jumangee/EcoSenseAtclock/EcosenseAtClock/mq4sensor_process.h

/**
 * MQ-4 process
 * for Processy Firmware Framework
 */
 
#ifndef _MQ4_SENSOR_PROCESS_H
#define _MQ4_SENSOR_PROCESS_H

#include "processy.h"
#include "processy_process.h"

#include "ecosense_cfg.h"
#include "mqsensor_process.h"

class MQ4SensorProcess: public MQSensorProcess {
	public:
		PROCESSID(PRC_MQ4);
		
		MQ4SensorProcess(IProcessMessage* msg);

		static IFirmwareProcess* factory(IProcessMessage* msg);

		IProcessMessage* getResultMsg();

};

#endif
