jumangee/EcoSenseAtclock/EcosenseAtClock/EspDrv/EspDrv.h

/*--------------------------------------------------------------------
This file is part of the Arduino WiFiEsp library.

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
You should have received a copy of the GNU General Public License
along with The Arduino WiFiEsp library.  If not, see
<http://www.gnu.org/licenses/>.
--------------------------------------------------------------------*/

#ifndef EspDrv_h
#define EspDrv_h

#include "Stream.h"
#include "IPAddress.h"


#include "RingBuffer.h"



// Maximum size of a SSID
#define WL_SSID_MAX_LENGTH 32

// Size of a MAC-address or BSSID
#define WL_MAC_ADDR_LENGTH 6

// Size of a MAC-address or BSSID
#define WL_IPV4_LENGTH 4

// Maximum size of a SSID list
#define WL_NETWORKS_LIST_MAXNUM	10

// Maxmium number of socket
#define	MAX_SOCK_NUM		4

// Socket not available constant
#define SOCK_NOT_AVAIL  255

// Default state value for Wifi state field
#define NA_STATE -1

#define WL_FW_VER_LENGTH 6

#define NO_SOCKET_AVAIL 255


// maximum size of AT command
#define CMD_BUFFER_SIZE 200


typedef enum eProtMode {TCP_MODE, UDP_MODE, SSL_MODE} tProtMode;


typedef enum {
        WL_FAILURE = -1,
        WL_SUCCESS = 1,
} wl_error_code_t;

/* Authentication modes */
enum wl_auth_mode {
        AUTH_MODE_INVALID,
        AUTH_MODE_AUTO,
        AUTH_MODE_OPEN_SYSTEM,
        AUTH_MODE_SHARED_KEY,
        AUTH_MODE_WPA,
        AUTH_MODE_WPA2,
        AUTH_MODE_WPA_PSK,
        AUTH_MODE_WPA2_PSK
};


typedef enum {
	WL_NO_SHIELD = 255,
	WL_IDLE_STATUS = 0,
	//WL_NO_SSID_AVAIL,
	//WL_SCAN_COMPLETED,
	WL_CONNECTED,
	WL_CONNECT_FAILED,
	//WL_CONNECTION_LOST,
	WL_DISCONNECTED
} wl_status_t;

/* Encryption modes */
enum wl_enc_type {
	ENC_TYPE_NONE = 0,
	ENC_TYPE_WEP = 1,
	ENC_TYPE_WPA_PSK = 2,
	ENC_TYPE_WPA2_PSK = 3,
	ENC_TYPE_WPA_WPA2_PSK = 4
};


enum wl_tcp_state {
	CLOSED      = 0,
	LISTEN      = 1,
	SYN_SENT    = 2,
	SYN_RCVD    = 3,
	ESTABLISHED = 4,
	FIN_WAIT_1  = 5,
	FIN_WAIT_2  = 6,
	CLOSE_WAIT  = 7,
	CLOSING     = 8,
	LAST_ACK    = 9,
	TIME_WAIT   = 10
};



class EspDrv
{

public:

    static void wifiDriverInit(Stream *espSerial);


    /* Start Wifi connection with passphrase
     *
     * param ssid: Pointer to the SSID string.
     * param passphrase: Passphrase. Valid characters in a passphrase must be between ASCII 32-126 (decimal).
     */
    static bool wifiConnect(const char* ssid, const char* passphrase);


    /*
	* Start the Access Point
	*/
	static bool wifiStartAP(const char* ssid, const char* pwd, uint8_t channel, uint8_t enc, uint8_t espMode);


    /*
	 * Set ip configuration disabling dhcp client
	 */
    //static void config(IPAddress local_ip);

    /*
	 * Set ip configuration disabling dhcp client
	 */
    //static void configAP(IPAddress local_ip);


    /*
     * Disconnect from the network
     *
     * return: WL_SUCCESS or WL_FAILURE
     */
    static int8_t disconnect();

    /*
     *
     *
     * return: one value of wl_status_t enum
     */
    static uint8_t getConnectionStatus();

    /*
     * Get the interface MAC address.
     *
     * return: pointer to uint8_t array with length WL_MAC_ADDR_LENGTH
     */
    //static uint8_t* getMacAddress();

    /*
     * Get the interface IP address.
     *
     * return: copy the ip address value in IPAddress object
     */
    /*static void getIpAddress(IPAddress& ip);

	static void getIpAddressAP(IPAddress& ip);*/

    /*
     * Get the interface IP netmask.
     * This can be used to retrieve settings configured through DHCP.
     *
     * return: true if successful
     */
    //static bool getNetmask(IPAddress& mask);

    /*
     * Get the interface IP gateway.
     * This can be used to retrieve settings configured through DHCP.
     *
     * return: true if successful
     */
    //static bool getGateway(IPAddress& mask);

    /*
     * Return the current SSID associated with the network
     *
     * return: ssid string
     */
    //static char* getCurrentSSID();

    /*
     * Return the current BSSID associated with the network.
     * It is the MAC address of the Access Point
     *
     * return: pointer to uint8_t array with length WL_MAC_ADDR_LENGTH
     */
    //static uint8_t* getCurrentBSSID();

    /*
     * Return the current RSSI /Received Signal Strength in dBm)
     * associated with the network
     *
     * return: signed value
     */
    static int32_t getCurrentRSSI();

    /*
     * Get the networks available
     *
     * return: Number of discovered networks
     */
    //static uint8_t getScanNetworks();

	/*
     * Return the SSID discovered during the network scan.
     *
     * param networkItem: specify from which network item want to get the information
	 *
     * return: ssid string of the specified item on the networks scanned list
     */
    //static char* getSSIDNetoworks(uint8_t networkItem);

    /*
     * Return the RSSI of the networks discovered during the scanNetworks
     *
     * param networkItem: specify from which network item want to get the information
	 *
     * return: signed value of RSSI of the specified item on the networks scanned list
     */
    //static int32_t getRSSINetoworks(uint8_t networkItem);

    /*
     * Return the encryption type of the networks discovered during the scanNetworks
     *
     * param networkItem: specify from which network item want to get the information
	 *
     * return: encryption type (enum wl_enc_type) of the specified item on the networks scanned list
     */
    //static uint8_t getEncTypeNetowrks(uint8_t networkItem);


    /*
     * Get the firmware version
     */
    static char* getFwVersion();


	////////////////////////////////////////////////////////////////////////////
	// Client/Server methods
	////////////////////////////////////////////////////////////////////////////


    //static bool startServer(uint16_t port, uint8_t sock);
    static bool startClient(const char* host, uint16_t port, uint8_t sock, uint8_t protMode);
    static void stopClient(uint8_t sock);
    //static uint8_t getServerState(uint8_t sock);
    static uint8_t getClientState(uint8_t sock);
    static bool getData(uint8_t connId, uint8_t *data, bool peek, bool* connClose);
    static int getDataBuf(uint8_t connId, uint8_t *buf, uint16_t bufSize);
    static bool sendData(uint8_t sock, const uint8_t *data, uint16_t len);
    static bool sendData(uint8_t sock, const __FlashStringHelper *data, uint16_t len, bool appendCrLf=false);
	static bool sendDataUdp(uint8_t sock, const char* host, uint16_t port, const uint8_t *data, uint16_t len);
    static uint16_t availData(uint8_t connId);


	static bool ping(const char *host);
    static void reset();

    //static void getRemoteIpAddress(IPAddress& ip);
    //static uint16_t getRemotePort();


////////////////////////////////////////////////////////////////////////////////

private:
	static Stream *espSerial;

	static long _bufPos;
	static uint8_t _connId;

	static uint16_t _remotePort;
	static uint8_t  _remoteIp[WL_IPV4_LENGTH];


	// firmware version string
	static char 	fwVersion[WL_FW_VER_LENGTH];

	// settings of requested network
	/*static char 	_networkSsid[WL_NETWORKS_LIST_MAXNUM][WL_SSID_MAX_LENGTH];
	static int32_t 	_networkRssi[WL_NETWORKS_LIST_MAXNUM];
	static uint8_t 	_networkEncr[WL_NETWORKS_LIST_MAXNUM];*/


	// settings of current selected network
	static char 	_ssid[WL_SSID_MAX_LENGTH];
	static uint8_t 	_bssid[WL_MAC_ADDR_LENGTH];
	static uint8_t 	_mac[WL_MAC_ADDR_LENGTH];
	static uint8_t  _localIp[WL_IPV4_LENGTH];


	// the ring buffer is used to search the tags in the stream
	static RingBuffer ringBuf;


	//static int sendCmd(const char* cmd, int timeout=1000);
	static int sendCmd(const __FlashStringHelper* cmd, int timeout=1000);
	static int sendCmd(const __FlashStringHelper* cmd, int timeout, ...);

	static bool sendCmdGet(const __FlashStringHelper* cmd, const char* startTag, const char* endTag, char* outStr, int outStrLen);
	static bool sendCmdGet(const __FlashStringHelper* cmd, const __FlashStringHelper* startTag, const __FlashStringHelper* endTag, char* outStr, int outStrLen);

	static int readUntil(unsigned int timeout, const char* tag=NULL, bool findTags=true);

	static void espEmptyBuf(bool warn=true);

	static int timedRead();


	/*friend class WiFiEsp;
	friend class WiFiEspServer;
	friend class WiFiEspClient;
	friend class WiFiEspUdp;*/
};

extern EspDrv espDrv;

#endif
