jumangee/EcoSenseAtclock/EcosenseAtClock/adcmux_mngmnt.h

#ifndef _ADCMUXMNGT_H
#define _ADCMUXMNGT_H

    #include <Arduino.h>
    #include "processy_cfg.h"
    #include "pinswitch_mngmnt.h"

    class ADCMuxManagement: protected PinSwitchManager {
        protected:
            ADCMuxManagement(byte *pins): PinSwitchManager(pins, 4) {
            }

            static ADCMuxManagement* instance;
            const static byte channelTruthTable[16][4];

        public:
            static ADCMuxManagement* get() {
                return ADCMuxManagement::instance;
            }

            static void init(const byte (&pins)[4]) {
                if (!ADCMuxManagement::instance) {
                    ADCMuxManagement::instance = new ADCMuxManagement(pins);
                }
            }

			uint32_t requestChannel(byte channel) {
				return PinSwitchManager::requestPin(channel);
			}

            bool release(uint32_t & key) {
                return PinSwitchManager::releasePin(key);
            }

        protected:
            void usePin(byte num);
    };

#endif
