jumangee/EcoSenseAtclock/EcosenseAtClock/simplesensor_process.h

/**
 * Base sensor process
 * for Processy Firmware Framework
 */

#ifndef _SIMPLE_SENSOR_PROCESS_H
#define _SIMPLE_SENSOR_PROCESS_H

#include "processy.h"
#include "processy_process.h"

#include "adcmuxchannel_process.h"

class SimpleSensorProcess: public ADCMuxChannelProcess {
	private:
		byte readingsCount;
        float value;

	public:
		SimpleSensorProcess(IProcessMessage* msg);

        float getValue() {
            return value / float(readingsCount);
        }

        virtual uint16_t getInstantValue() = 0;

        /**
         * Calc V from analog value
         */
        float getVoltage() {
            return getValue() * (5.0 / 1023.0);
        }

		bool readingsDone(byte countPerResult) {
			if (readingsCount >= countPerResult) {
				this->readingsCount = 0;
				this->value = 0;
			}
	
			this->value += this->getInstantValue();
			this->readingsCount++;

			return (readingsCount >= countPerResult) ? true : false;
		}
};

#endif
